gianlucarenzi/A1200KB/PlatePCB/amiga-keyboard-a500-a1200-bigass.png

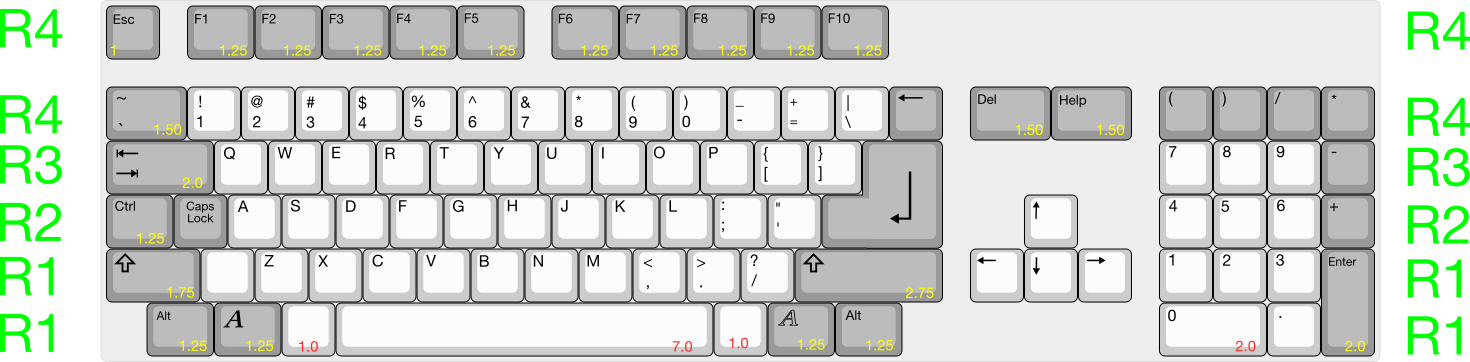
PlatePCB/amiga-keyboard-a500-a1200-bigass.png
