gianlucarenzi/A1200KB/3Dfiles/A1200.net case/rev3/Right base support.stl

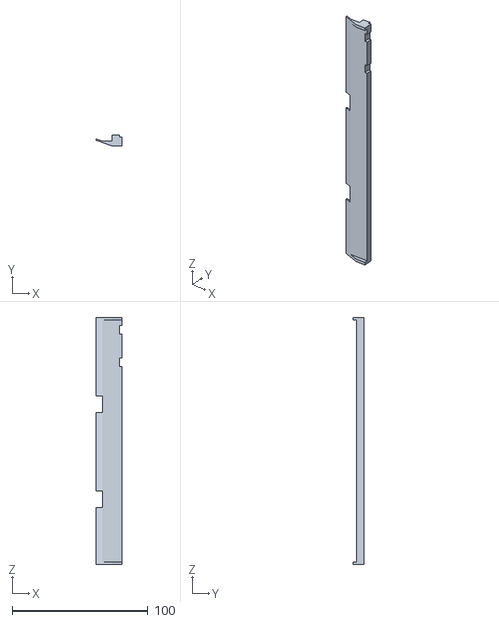
[picture p18: CAD file, 2023-02-19, an earlier design]
3Dfiles/A1200.net case/rev3/Right base support.stl
19.2 x 8.05 x 182.0
