gianlucarenzi/A1200KB/3Dfiles/A1200.net case/rev3/Brace insulator and spacer.stl

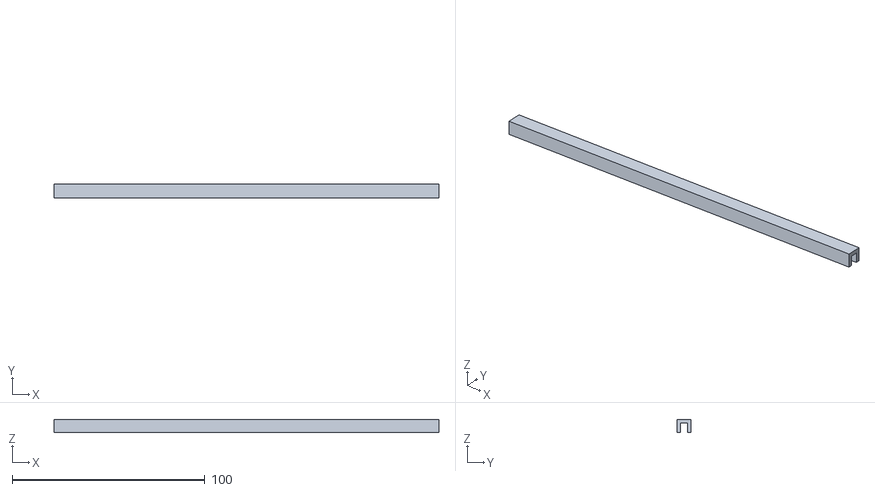
[picture p19: CAD file, 2023-02-19, an earlier design]
3Dfiles/A1200.net case/rev3/Brace insulator and spacer.stl
200.0 x 7.50 x 7.00
