gianlucarenzi/A1200KB/amiga_usb_mx/Core/Inc/host_driver.h

/*
Copyright 2011 Jun Wako <wakojun@gmail.com>

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
You should have received a copy of the GNU General Public License
along with this program.  If not, see <http://www.gnu.org/licenses/>.
*/

#ifndef HOST_DRIVER_H
#define HOST_DRIVER_H

#include <stdint.h>
#include "report.h"


typedef struct {
    uint8_t (*keyboard_leds)(void);
    void (*send_keyboard)(report_keyboard_t *);
    void (*send_mouse)(report_mouse_t *);
    void (*send_system)(uint16_t);
    void (*send_consumer)(uint16_t);
} host_driver_t;

#endif
