gianlucarenzi/A1200KB/amiga_usb_mx/Core/Src/action.c

/*
Copyright 2012,2013,2020 Jun Wako <wakojun@gmail.com>

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
You should have received a copy of the GNU General Public License
along with this program.  If not, see <http://www.gnu.org/licenses/>.
*/
#include "host.h"
#include "keycode.h"
#include "keyboard.h"
#include "mousekey.h"
#include "command.h"
#include "led.h"
#include "backlight.h"
#include "action_layer.h"
#include "action_tapping.h"
#include "action_macro.h"
#include "action_util.h"
#include "action.h"
#include "hook.h"
#include "wait.h"
#include "bootloader.h"

#ifdef DEBUG_ACTION
#include "debug.h"
#else
#include "nodebug.h"
#endif

static int debuglevel = DBG_INFO;

void action_exec(keyevent_t event)
{
    if (!IS_NOEVENT(event)) {
        dprint("EVENT: "); debug_event(event); dprintln();
        DBG_N("\r\n---- action_exec: start -----\r\n");
        DBG_N("EVENT: "); debug_event(event); dprintln();
        /*
         * This seems to be a BUG:
         * https://github.com/tmk/tmk_keyboard/blob/6271878a021fcf578b71e2b7e97cd43786efa7dd/tmk_core/common/action.c#L45
         */
        //hook_matrix_change(event);
    }

    keyrecord_t record = { .event = event };

#ifndef NO_ACTION_TAPPING
    action_tapping_process(record);
#else
    process_action(&record);
    if (!IS_NOEVENT(record.event)) {
        dprint("processed: "); debug_record(record); dprintln();
    }
#endif
}

void process_action(keyrecord_t *record)
{
	DBG_N("Called with %p\r\n", record);
    if (hook_process_action(record)) return;

    keyevent_t event = record->event;
#ifndef NO_ACTION_TAPPING
    uint8_t tap_count = record->tap.count;
#endif

    if (IS_NOEVENT(event)) {
    	DBG_N("No EVENT\r\n");
    	return;
    }

    action_t action = layer_switch_get_action(event);
    dprint("ACTION: "); debug_action(action);
#ifndef NO_ACTION_LAYER
    dprint(" layer_state: "); layer_debug();
    dprint(" default_layer_state: "); default_layer_debug();
#endif
    dprintln();

    DBG_N("SWITCH ACTION.KIND.ID %d\r\n", action.kind.id);
    switch (action.kind.id) {
        /* Key and Mods */
        case ACT_LMODS:
        case ACT_RMODS:
            {
                uint8_t mods = (action.kind.id == ACT_LMODS) ?  action.key.mods :
                                                                action.key.mods<<4;
                DBG_N("ACT_RMODS/ACT_RMODS: mods %d\r\n", mods);
                if (event.pressed) {
                    if (mods) {
                        add_weak_mods(mods);
                        send_keyboard_report();
                    }
                    register_code(action.key.code);
                } else {
                    unregister_code(action.key.code);
                    if (mods) {
                        del_weak_mods(mods);
                        send_keyboard_report();
                    }
                }
            }
            break;
#ifndef NO_ACTION_TAPPING
        case ACT_LMODS_TAP:
        case ACT_RMODS_TAP:
            {
                uint8_t mods = (action.kind.id == ACT_LMODS_TAP) ?  action.key.mods :
                                                                    action.key.mods<<4;
                switch (action.key.code) {
    #ifndef NO_ACTION_ONESHOT
                    case MODS_ONESHOT:
                        // Oneshot modifier
                        if (event.pressed) {
                            if (tap_count == 0) {
                                register_mods(mods);
                            }
                            else if (tap_count == 1) {
                                dprint("MODS_TAP: Oneshot: start\n");
                                set_oneshot_mods(mods);
                            }
                            else {
                                register_mods(mods);
                            }
                        } else {
                            if (tap_count == 0) {
                                clear_oneshot_mods();
                                unregister_mods(mods);
                            }
                            else if (tap_count == 1) {
                                // Retain Oneshot mods
                            }
                            else {
                                clear_oneshot_mods();
                                unregister_mods(mods);
                            }
                        }
                        break;
    #endif
                    case MODS_TAP_TOGGLE:
                        if (event.pressed) {
                            if (tap_count <= TAPPING_TOGGLE) {
                                if (mods & get_mods()) {
                                    dprint("MODS_TAP_TOGGLE: toggle mods off\n");
                                    unregister_mods(mods);
                                } else {
                                    dprint("MODS_TAP_TOGGLE: toggle mods on\n");
                                    register_mods(mods);
                                }
                            }
                        } else {
                            if (tap_count < TAPPING_TOGGLE) {
                                dprint("MODS_TAP_TOGGLE: release : unregister_mods\n");
                                unregister_mods(mods);
                            }
                        }
                        break;
                    default:
                        if (event.pressed) {
                            if (tap_count > 0) {
                                if (record->tap.interrupted) {
                                    dprint("MODS_TAP: Tap: Cancel: add_mods\n");
                                    // ad hoc: set 0 to cancel tap
                                    record->tap.count = 0;
                                    register_mods(mods);
                                } else {
                                    dprint("MODS_TAP: Tap: register_code\n");
                                    register_code(action.key.code);

                                    // Delay for MacOS #659
                                    if (action.key.code == KC_CAPSLOCK ||
                                            action.key.code == KC_NUMLOCK ||
                                            action.key.code == KC_SCROLLLOCK) {
                                        wait_ms(100);
                                    }
                                }
                            } else {
                                dprint("MODS_TAP: No tap: add_mods\n");
                                register_mods(mods);
                            }
                        } else {
                            if (tap_count > 0) {
                                dprint("MODS_TAP: Tap: unregister_code\n");
                                unregister_code(action.key.code);
                            } else {
                                dprint("MODS_TAP: No tap: add_mods\n");
                                unregister_mods(mods);
                            }
                        }
                        break;
                }
            }
            break;
#endif
#ifdef EXTRAKEY_ENABLE
        /* other HID usage */
        case ACT_USAGE:
            switch (action.usage.page) {
                case PAGE_SYSTEM:
                    if (event.pressed) {
                        host_system_send(action.usage.code);
                    } else {
                        host_system_send(0);
                    }
                    break;
                case PAGE_CONSUMER:
                    if (event.pressed) {
                        host_consumer_send(action.usage.code);
                    } else {
                        host_consumer_send(0);
                    }
                    break;
            }
            break;
#endif
#ifdef MOUSEKEY_ENABLE
        /* Mouse key */
        case ACT_MOUSEKEY:
            if (event.pressed) {
                mousekey_on(action.key.code);
                mousekey_send();
            } else {
                mousekey_off(action.key.code);
                mousekey_send();
            }
            break;
#endif
#ifndef NO_ACTION_LAYER
        case ACT_LAYER:
            if (action.layer_bitop.on == 0) {
                /* Default Layer Bitwise Operation */
                if (!event.pressed) {
                    uint8_t shift = action.layer_bitop.part*4;
                    uint32_t bits = ((uint32_t)action.layer_bitop.bits)<<shift;
                    uint32_t mask = (action.layer_bitop.xbit) ? ~(((uint32_t)0xf)<<shift) : 0;
                    switch (action.layer_bitop.op) {
                        case OP_BIT_AND: default_layer_and(bits | mask); break;
                        case OP_BIT_OR:  default_layer_or(bits | mask);  break;
                        case OP_BIT_XOR: default_layer_xor(bits | mask); break;
                        case OP_BIT_SET: default_layer_and(mask); default_layer_or(bits); break;
                    }
                }
            } else {
                /* Layer Bitwise Operation */
                if (event.pressed ? (action.layer_bitop.on & ON_PRESS) :
                                    (action.layer_bitop.on & ON_RELEASE)) {
                    uint8_t shift = action.layer_bitop.part*4;
                    uint32_t bits = ((uint32_t)action.layer_bitop.bits)<<shift;
                    uint32_t mask = (action.layer_bitop.xbit) ? ~(((uint32_t)0xf)<<shift) : 0;
                    switch (action.layer_bitop.op) {
                        case OP_BIT_AND: layer_and(bits | mask); break;
                        case OP_BIT_OR:  layer_or(bits | mask);  break;
                        case OP_BIT_XOR: layer_xor(bits | mask); break;
                        case OP_BIT_SET: layer_and(mask); layer_or(bits); break;
                    }
                }
            }
            break;
    #ifndef NO_ACTION_TAPPING
        case ACT_LAYER_TAP:
        case ACT_LAYER_TAP_EXT:
            switch (action.layer_tap.code) {
                case 0xc0 ... 0xdf:
                    /* layer On/Off with modifiers */
                    if (event.pressed) {
                        layer_on(action.layer_tap.val);
                        register_mods((action.layer_tap.code & 0x10) ?
                                (action.layer_tap.code & 0x0f) << 4 :
                                (action.layer_tap.code & 0x0f));
                    } else {
                        layer_off(action.layer_tap.val);
                        unregister_mods((action.layer_tap.code & 0x10) ?
                                (action.layer_tap.code & 0x0f) << 4 :
                                (action.layer_tap.code & 0x0f));
                    }
                    break;
                case OP_TAP_TOGGLE:
                    /* tap toggle */
                    if (event.pressed) {
                        if (tap_count < TAPPING_TOGGLE) {
                            layer_invert(action.layer_tap.val);
                        }
                    } else {
                        if (tap_count <= TAPPING_TOGGLE) {
                            layer_invert(action.layer_tap.val);
                        }
                    }
                    break;
                case OP_ON_OFF:
                    event.pressed ? layer_on(action.layer_tap.val) :
                                    layer_off(action.layer_tap.val);
                    break;
                case OP_OFF_ON:
                    event.pressed ? layer_off(action.layer_tap.val) :
                                    layer_on(action.layer_tap.val);
                    break;
                case OP_SET_CLEAR:
                    event.pressed ? layer_move(action.layer_tap.val) :
                                    layer_clear();
                    break;
                default:
                    /* tap key */
                    if (event.pressed) {
                        if (tap_count > 0) {
                            dprint("KEYMAP_TAP_KEY: Tap: register_code\n");
                            register_code(action.layer_tap.code);

                            // Delay for MacOS #659
                            if (action.layer_tap.code == KC_CAPSLOCK ||
                                    action.layer_tap.code == KC_NUMLOCK ||
                                    action.layer_tap.code == KC_SCROLLLOCK) {
                                wait_ms(100);
                            }
                        } else {
                            dprint("KEYMAP_TAP_KEY: No tap: On on press\n");
                            layer_on(action.layer_tap.val);
                        }
                    } else {
                        if (tap_count > 0) {
                            dprint("KEYMAP_TAP_KEY: Tap: unregister_code\n");
                            unregister_code(action.layer_tap.code);
                        } else {
                            dprint("KEYMAP_TAP_KEY: No tap: Off on release\n");
                            layer_off(action.layer_tap.val);
                        }
                    }
                    break;
            }
            break;
    #endif
#endif
        /* Extentions */
#ifndef NO_ACTION_MACRO
        case ACT_MACRO:
            action_macro_play(action_get_macro(record, action.func.id, action.func.opt));
            break;
#endif
#ifdef BACKLIGHT_ENABLE
        case ACT_BACKLIGHT:
            if (!event.pressed) {
                switch (action.backlight.opt) {
                    case BACKLIGHT_INCREASE:
                        backlight_increase();
                        break;
                    case BACKLIGHT_DECREASE:
                        backlight_decrease();
                        break;
                    case BACKLIGHT_TOGGLE:
                        backlight_toggle();
                        break;
                    case BACKLIGHT_STEP:
                        backlight_step();
                        break;
                    case BACKLIGHT_LEVEL:
                        backlight_level(action.backlight.level);
                        break;
                }
            }
            break;
#endif
        case ACT_COMMAND:
            switch (action.command.id) {
                case COMMAND_BOOTLOADER:
                    if (event.pressed) {
                        clear_keyboard();
                        wait_ms(50);
                        bootloader_jump();
                    }
                    break;
            }
            break;
#ifndef NO_ACTION_FUNCTION
        case ACT_FUNCTION:
            action_function(record, action.func.id, action.func.opt);
            break;
#endif
        default:
            break;
    }
}




/*
 * Utilities for actions.
 */
void register_code(uint8_t code)
{
	DBG_N("Called with: %d\r\n", code);
    if (code == KC_NO) {
        return;
    }

#ifdef LOCKING_SUPPORT_ENABLE
    else if (code == KC_LOCKING_CAPS ||
                code == KC_LOCKING_NUM ||
                code == KC_LOCKING_SCROLL) {
        uint8_t c, l;
        if (code == KC_LOCKING_CAPS) {
            c = KC_CAPSLOCK;
            l = 1<<USB_LED_CAPS_LOCK;
        } else if (code == KC_LOCKING_NUM) {
            c = KC_NUMLOCK;
            l = 1<<USB_LED_NUM_LOCK;
        } else if (code == KC_LOCKING_SCROLL) {
            c = KC_SCROLLLOCK;
            l = 1<<USB_LED_SCROLL_LOCK;
        }
#ifdef LOCKING_RESYNC_ENABLE
        // Resync: ignore if lock indicator is already on
        if (host_keyboard_leds() & l) return;
#endif
        add_key(c);
        send_keyboard_report();
        wait_ms(100); // Delay for MacOS #390
        del_key(c);
        send_keyboard_report();
    }
#endif

    else if IS_KEY(code) {
        // TODO: should push command_proc out of this block?
        if (command_proc(code)) return;

#ifndef NO_ACTION_ONESHOT
/* TODO: remove
        if (oneshot_state.mods && !oneshot_state.disabled) {
            uint8_t tmp_mods = get_mods();
            add_mods(oneshot_state.mods);

            add_key(code);
            send_keyboard_report();

            set_mods(tmp_mods);
            send_keyboard_report();
            oneshot_cancel();
        } else
*/
#endif
        {
            add_key(code);
            send_keyboard_report();
        }
    }
    else if IS_MOD(code) {
        add_mods(MOD_BIT(code));
        send_keyboard_report();
    }
    else if IS_SYSTEM(code) {
        host_system_send(KEYCODE2SYSTEM(code));
    }
    else if IS_CONSUMER(code) {
        host_consumer_send(KEYCODE2CONSUMER(code));
    }
}

void unregister_code(uint8_t code)
{
	DBG_N("Called with: %d\r\n", code);
    if (code == KC_NO) {
        return;
    }

#ifdef LOCKING_SUPPORT_ENABLE
    else if (code == KC_LOCKING_CAPS ||
                code == KC_LOCKING_NUM ||
                code == KC_LOCKING_SCROLL) {
        uint8_t c, l;
        if (code == KC_LOCKING_CAPS) {
            c = KC_CAPSLOCK;
            l = 1<<USB_LED_CAPS_LOCK;
        } else if (code == KC_LOCKING_NUM) {
            c = KC_NUMLOCK;
            l = 1<<USB_LED_NUM_LOCK;
        } else if (code == KC_LOCKING_SCROLL) {
            c = KC_SCROLLLOCK;
            l = 1<<USB_LED_SCROLL_LOCK;
        }
#ifdef LOCKING_RESYNC_ENABLE
        // Resync: ignore if lock indicator is already off
        if (!(host_keyboard_leds() & l)) return;
#endif
        add_key(c);
        send_keyboard_report();
        wait_ms(100); // Delay for MacOS #390
        del_key(c);
        send_keyboard_report();
    }
#endif

    else if IS_KEY(code) {
        del_key(code);
        send_keyboard_report();
    }
    else if IS_MOD(code) {
        del_mods(MOD_BIT(code));
        send_keyboard_report();
    }
    else if IS_SYSTEM(code) {
        host_system_send(0);
    }
    else if IS_CONSUMER(code) {
        host_consumer_send(0);
    }
}

void type_code(uint8_t code)
{
    register_code(code);
    unregister_code(code);
}

void register_mods(uint8_t mods)
{
	DBG_N("Called with: %d\r\n", mods);
    if (mods) {
        add_mods(mods);
        send_keyboard_report();
    }
}

void unregister_mods(uint8_t mods)
{
	DBG_N("Called with: %d\r\n", mods);
    if (mods) {
        del_mods(mods);
        send_keyboard_report();
    }
}

void clear_keyboard(void)
{
    clear_mods();
    clear_keyboard_but_mods();
}

void clear_keyboard_but_mods(void)
{
	DBG_N("Called\r\n");
    clear_weak_mods();
    clear_keys();
    send_keyboard_report();
#ifdef MOUSEKEY_ENABLE
    mousekey_clear();
    mousekey_send();
#endif
#ifdef EXTRAKEY_ENABLE
    host_system_send(0);
    host_consumer_send(0);
#endif
}

bool is_tap_key(keyevent_t event)
{
    if (IS_NOEVENT(event)) { return false; }

    action_t action = layer_switch_get_action(event);

    switch (action.kind.id) {
        case ACT_LMODS_TAP:
        case ACT_RMODS_TAP:
            switch (action.key.code) {
                case MODS_ONESHOT:
                case MODS_TAP_TOGGLE:
                case KC_A ... KC_EXSEL:                 // tap key
                case KC_LCTRL ... KC_RGUI:              // tap key
                    return true;
            }
        case ACT_LAYER_TAP:
        case ACT_LAYER_TAP_EXT:
            switch (action.layer_tap.code) {
                case 0xc0 ... 0xdf:         // with modifiers
                    return false;
                case KC_A ... KC_EXSEL:     // tap key
                case KC_LCTRL ... KC_RGUI:  // tap key
                case OP_TAP_TOGGLE:
                    return true;
            }
            return false;
        case ACT_MACRO:
        case ACT_FUNCTION:
            if (action.func.opt & FUNC_TAP) { return true; }
            return false;
    }
    return false;
}


/*
 * debug print
 */
void debug_event(keyevent_t event)
{
    dprintf("%04X%c(%u)", (event.key.row<<8 | event.key.col), (event.pressed ? 'd' : 'u'), event.time);
    DBG_N("%04X%c(%u)\r\n", (event.key.row<<8 | event.key.col), (event.pressed ? 'd' : 'u'), event.time);
}

void debug_record(keyrecord_t record)
{
    debug_event(record.event);
#ifndef NO_ACTION_TAPPING
    dprintf(":%u%c", record.tap.count, (record.tap.interrupted ? '-' : ' '));
#endif
}

void debug_action(action_t action)
{
    switch (action.kind.id) {
        case ACT_LMODS:             dprint("ACT_LMODS");             break;
        case ACT_RMODS:             dprint("ACT_RMODS");             break;
        case ACT_LMODS_TAP:         dprint("ACT_LMODS_TAP");         break;
        case ACT_RMODS_TAP:         dprint("ACT_RMODS_TAP");         break;
        case ACT_USAGE:             dprint("ACT_USAGE");             break;
        case ACT_MOUSEKEY:          dprint("ACT_MOUSEKEY");          break;
        case ACT_LAYER:             dprint("ACT_LAYER");             break;
        case ACT_LAYER_TAP:         dprint("ACT_LAYER_TAP");         break;
        case ACT_LAYER_TAP_EXT:     dprint("ACT_LAYER_TAP_EXT");     break;
        case ACT_MACRO:             dprint("ACT_MACRO");             break;
        case ACT_COMMAND:           dprint("ACT_COMMAND");           break;
        case ACT_FUNCTION:          dprint("ACT_FUNCTION");          break;
        default:                    dprint("UNKNOWN");               break;
    }
    dprintf("[%X:%02X]", action.kind.param>>8, action.kind.param&0xff);
}
