gianlucarenzi/A1200KB/amiga_usb_mx/Core/Inc/print.h

/* Copyright 2012 Jun Wako <wakojun@gmail.com> */
/* Very basic print functions, intended to be used with usb_debug_only.c
 * http://www.pjrc.com/teensy/
 * Copyright (c) 2008 PJRC.COM, LLC
 *
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
 * THE SOFTWARE IS PROVIDED "AS IS", WITHOUT WARRANTY OF ANY KIND, EXPRESS OR
 * IMPLIED, INCLUDING BUT NOT LIMITED TO THE WARRANTIES OF MERCHANTABILITY,
 * FITNESS FOR A PARTICULAR PURPOSE AND NONINFRINGEMENT. IN NO EVENT SHALL THE
 * AUTHORS OR COPYRIGHT HOLDERS BE LIABLE FOR ANY CLAIM, DAMAGES OR OTHER
 * LIABILITY, WHETHER IN AN ACTION OF CONTRACT, TORT OR OTHERWISE, ARISING FROM,
 * OUT OF OR IN CONNECTION WITH THE SOFTWARE OR THE USE OR OTHER DEALINGS IN
 * THE SOFTWARE.
 */

#ifndef PRINT_H__
#define PRINT_H__ 1

#include <stdint.h>
#include <stdbool.h>
#include "util.h"




#ifndef NO_PRINT


#if defined(__AVR__)

	#include "avr/xprintf.h"
	#define print(s)    xputs(PSTR(s))
	#define println(s)  xputs(PSTR(s "\r\n"))

	#ifdef __cplusplus
	extern "C"
	#endif
	/* function pointer of sendchar to be used by print utility */
	void print_set_sendchar(int8_t (*print_sendchar_func)(uint8_t));

#elif defined(PROTOCOL_CHIBIOS) /* __AVR__ */

	#include "chibios/printf.h"

	#define print(s)    printf(s)
	#define println(s)  printf(s "\r\n")
	#define xprintf  printf

#elif defined(__arm__) /* __AVR__ */

	#define xprintf(fmt, args...) printf(fmt, ## args)
	#define print(s)    xprintf(s)
	#define println(s)  xprintf(s "\r\n")

	/* TODO: to select output destinations: UART/USBSerial */
	#define print_set_sendchar(func)

#endif /* __AVR__ */


/* decimal */
#define print_dec(i)                xprintf("%u", i)
#define print_decs(i)               xprintf("%d", i)
/* hex */
#define print_hex4(i)               xprintf("%X", i)
#define print_hex8(i)               xprintf("%02X", i)
#define print_hex16(i)              xprintf("%04X", i)
#define print_hex32(i)              xprintf("%08lX", i)
/* binary */
#ifdef __AVR__
#define print_bin4(i)               xprintf("%04b", i)
#define print_bin8(i)               xprintf("%08b", i)
#define print_bin16(i)              xprintf("%016b", i)
#define print_bin32(i)              xprintf("%032lb", i)
#define print_bin_reverse8(i)       xprintf("%08b", bitrev(i))
#define print_bin_reverse16(i)      xprintf("%016b", bitrev(i))
#define print_bin_reverse32(i)      xprintf("%032lb", bitrev(i))
#define print_val_bin8(v)           xprintf(#v ": %08b\n", v)
#define print_val_bin16(v)          xprintf(#v ": %016b\n", v)
#define print_val_bin32(v)          xprintf(#v ": %032lb\n", v)
#define print_val_bin_reverse8(v)   xprintf(#v ": %08b\n", bitrev(v))
#define print_val_bin_reverse16(v)  xprintf(#v ": %016b\n", bitrev16(v))
#define print_val_bin_reverse32(v)  xprintf(#v ": %032lb\n", bitrev32(v))
#endif
#ifdef __arm__
extern void xprintfbin(uint32_t val, int n_bits);
extern void xprintfbin_rev(uint32_t val, int n_bits);
#define print_bin4(i)               xprintfbin(i, 4)
#define print_bin8(i)               xprintfbin(i, 8)
#define print_bin16(i)              xprintfbin(i, 16)
#define print_bin32(i)              xprintfbin(i, 32)
#define print_bin_reverse8(i)       xprintfbin_rev(i, 8)
#define print_bin_reverse16(i)      xprintfbin_rev(i, 16)
#define print_bin_reverse32(i)      xprintfbin_rev(i, 32)
#endif
/* print value utility */
#define print_val_dec(v)            xprintf(#v ": %u\n", v)
#define print_val_decs(v)           xprintf(#v ": %d\n", v)
#define print_val_hex8(v)           xprintf(#v ": %X\n", v)
#define print_val_hex16(v)          xprintf(#v ": %02X\n", v)
#define print_val_hex32(v)          xprintf(#v ": %04lX\n", v)

#else   /* NO_PRINT */

#define xprintf(s,...)              ((void)0)
#define print(s)                    ((void)0)
#define println(s)                  ((void)0)
#define print_set_sendchar(func)    ((void)0)
#define print_dec(data)             ((void)0)
#define print_decs(data)            ((void)0)
#define print_hex4(data)            ((void)0)
#define print_hex8(data)            ((void)0)
#define print_hex16(data)           ((void)0)
#define print_hex32(data)           ((void)0)
#define print_bin4(data)            ((void)0)
#define print_bin8(data)            ((void)0)
#define print_bin16(data)           ((void)0)
#define print_bin32(data)           ((void)0)
#define print_bin_reverse8(data)    ((void)0)
#define print_bin_reverse16(data)   ((void)0)
#define print_bin_reverse32(data)   ((void)0)
#define print_val_dec(v)            ((void)0)
#define print_val_decs(v)           ((void)0)
#define print_val_hex8(v)           ((void)0)
#define print_val_hex16(v)          ((void)0)
#define print_val_hex32(v)          ((void)0)
#define print_val_bin8(v)           ((void)0)
#define print_val_bin16(v)          ((void)0)
#define print_val_bin32(v)          ((void)0)
#define print_val_bin_reverse8(v)   ((void)0)
#define print_val_bin_reverse16(v)  ((void)0)
#define print_val_bin_reverse32(v)  ((void)0)
#define init_printf(s,ss)           ((void)0)

#endif  /* NO_PRINT */


/* Backward compatiblitly for old name */
#define pdec(data)              print_dec(data)
#define pdec16(data)            print_dec(data)
#define phex(data)              print_hex8(data)
#define phex16(data)            print_hex16(data)
#define pbin(data)              print_bin8(data)
#define pbin16(data)            print_bin16(data)
#define pbin_reverse(data)      print_bin_reverse8(data)
#define pbin_reverse16(data)    print_bin_reverse16(data)


#endif
