gianlucarenzi/A1200KB/amiga_usb_mx/Core/Inc/debug.h

/*
 * $Id: debug.h,v 1.1 2016/01/12 09:17:22 gianluca Exp $
 */
#ifndef __DEBUG_H__
#define __DEBUG_H__

#include <stdio.h>
#include <stdint.h>
#include <stdbool.h>
#include "print.h"

#ifdef __cplusplus
extern "C" {
#endif

/*
 * Debug output control
 */
typedef union {
	struct {
		bool enable:1;
		bool matrix:1;
		bool keyboard:1;
		bool mouse:1;
		uint8_t reserved:4;
	};
	uint8_t raw;
} debug_config_t;

extern debug_config_t debug_config;

#ifdef __cplusplus
}
#endif

/* for backward compatibility */
#define debug_enable    (debug_config.enable)
#define debug_matrix    (debug_config.matrix)
#define debug_keyboard  (debug_config.keyboard)
#define debug_mouse     (debug_config.mouse)


/*
 * Debug print utils
 */
#ifndef NO_DEBUG

#define dprint(s)                   do { if (debug_enable) print(s); } while (0)
#define dprintln(s)                 do { if (debug_enable) println(s); } while (0)
#define dprintf(fmt, ...)           do { if (debug_enable) xprintf(fmt, ##__VA_ARGS__); } while (0)
#define dmsg(s)                     dprintf("%s at %s: %S\n", __FILE__, __LINE__, PSTR(s))

/* Deprecated. DO NOT USE these anymore, use dprintf instead. */
#define debug(s)                    do { if (debug_enable) print(s); } while (0)
#define debugln(s)                  do { if (debug_enable) println(s); } while (0)
#define debug_msg(s)                do { \
    if (debug_enable) { \
        print(__FILE__); print(" at "); print_dec(__LINE__); print(" in "); print(": "); print(s); \
    } \
} while (0)
#define debug_dec(data)             do { if (debug_enable) print_dec(data); } while (0)
#define debug_decs(data)            do { if (debug_enable) print_decs(data); } while (0)
#define debug_hex4(data)            do { if (debug_enable) print_hex4(data); } while (0)
#define debug_hex8(data)            do { if (debug_enable) print_hex8(data); } while (0)
#define debug_hex16(data)           do { if (debug_enable) print_hex16(data); } while (0)
#define debug_hex32(data)           do { if (debug_enable) print_hex32(data); } while (0)
#define debug_bin8(data)            do { if (debug_enable) print_bin8(data); } while (0)
#define debug_bin16(data)           do { if (debug_enable) print_bin16(data); } while (0)
#define debug_bin32(data)           do { if (debug_enable) print_bin32(data); } while (0)
#define debug_bin_reverse8(data)    do { if (debug_enable) print_bin_reverse8(data); } while (0)
#define debug_bin_reverse16(data)   do { if (debug_enable) print_bin_reverse16(data); } while (0)
#define debug_bin_reverse32(data)   do { if (debug_enable) print_bin_reverse32(data); } while (0)
#define debug_hex(data)             debug_hex8(data)
#define debug_bin(data)             debug_bin8(data)
#define debug_bin_reverse(data)     debug_bin8(data)

#else /* NO_DEBUG */

#define dprint(s)                   ((void)0)
#define dprintln(s)                 ((void)0)
#define dprintf(fmt, ...)           ((void)0)
#define dmsg(s)                     ((void)0)
#define debug(s)                    ((void)0)
#define debugln(s)                  ((void)0)
#define debug_msg(s)                ((void)0)
#define debug_dec(data)             ((void)0)
#define debug_decs(data)            ((void)0)
#define debug_hex4(data)            ((void)0)
#define debug_hex8(data)            ((void)0)
#define debug_hex16(data)           ((void)0)
#define debug_hex32(data)           ((void)0)
#define debug_bin8(data)            ((void)0)
#define debug_bin16(data)           ((void)0)
#define debug_bin32(data)           ((void)0)
#define debug_bin_reverse8(data)    ((void)0)
#define debug_bin_reverse16(data)   ((void)0)
#define debug_bin_reverse32(data)   ((void)0)
#define debug_hex(data)             ((void)0)
#define debug_bin(data)             ((void)0)
#define debug_bin_reverse(data)     ((void)0)

#endif /* NO_DEBUG */

/* ANSI Eye-Candy ;-) */
#define ANSI_RED    "\x1b[31m"
#define ANSI_GREEN  "\x1b[32m"
#define ANSI_YELLOW "\x1b[1;33m"
#define ANSI_BLUE   "\x1b[1;34m"
#define ANSI_RESET  "\x1b[0m"

#define printR(fmt, args...) \
	{\
		printf(fmt, ## args); \
	}

#define printRaw(type, fmt, args...) \
	{\
		printf("%s " type " (%s): " fmt, __FILE__, __func__, ## args); \
	}

#define DBG_N(fmt, args...) \
  { if (debuglevel >= DBG_NOISY) {\
		printf(ANSI_YELLOW); \
		printRaw("NOISY", fmt,## args); \
		printf(ANSI_RESET); \
	} \
  }

#define DBG_V(fmt, args...) \
  { if (debuglevel >= DBG_VERBOSE) {\
		printf(ANSI_BLUE); \
		printRaw("VERBOSE", fmt,## args); \
		printf(ANSI_RESET); \
	} \
  }

#define DBG_I(fmt, args...) \
  { if (debuglevel >= DBG_INFO) {\
		printf(ANSI_GREEN); \
		printRaw("INFO", fmt,## args); \
		printf(ANSI_RESET); \
	} \
  }

#define DBG_E(fmt, args...) \
  { \
	printf(ANSI_RED); \
	printRaw("ERR", fmt, ## args); \
	printf(ANSI_RESET); \
  }

#define DBG_ERROR   0
#define DBG_INFO    1
#define DBG_VERBOSE 2
#define DBG_NOISY   3

#ifdef __cplusplus
}
#endif

#endif
