gianlucarenzi/A1200KB/amiga_usb_mx/Core/Src/syscall.c

#include <errno.h>
#include <sys/unistd.h> // STDOUT_FILENO, STDERR_FILENO
#include "syscall.h"
#include <stm32f4xx_hal.h> // per HAL_StatusTypeDef
#include "debug.h"

static t_syscall_status uart_initialize = SYSCALL_NOTREADY;
static UART_HandleTypeDef *uart = NULL;
static int debuglevel = DBG_ERROR;

void _write_ready(t_syscall_status rdy, UART_HandleTypeDef *ptr)
{
	if (ptr != NULL)
	{
		uart_initialize = rdy;
		uart = ptr;
	}
}

int _write(int file, char *data, int len)
{
	HAL_StatusTypeDef status = HAL_OK - 1;

	if ((file != STDOUT_FILENO) && (file != STDERR_FILENO))
	{
		errno = EBADF;
		return -1;
	}

	if (uart_initialize == SYSCALL_READY)
	{
		if (uart != NULL)
		{
			// arbitrary timeout 1000
			status = HAL_UART_Transmit(uart, (uint8_t*)data, len, 1000);
		}
	}

	// return # of bytes written - as best we can tell
	return (status == HAL_OK ? len : 0);
}

static uint32_t timertick_start_ms = 0;
void timer_start(void)
{
	// When timer starts get the realtime system tick
	timertick_start_ms = HAL_GetTick();
}

// I hate this delay because they are clockspeed dependent!!!
#define delayUS_ASM(us) do {\
	asm volatile (	"MOV R0,%[loops]\n\t"\
			"1: \n\t"\
			"SUB R0, #1\n\t"\
			"CMP R0, #0\n\t"\
			"BNE 1b \n\t" : : [loops] "r" (16*us) : "memory"\
		      );\
} while(0)

void udelay(uint32_t micros)
{
	DBG_N("Enter with: %lu\n", micros);
	if (micros > 0)
	{
		/* Go to number of cycles for system */
		DBG_N("MICROS: %lu\r\n", micros);
		delayUS_ASM(micros);
	}
	DBG_N("Exit\r\n");
}

void mdelay(uint32_t millis)
{
	HAL_Delay(millis);
}
