gianlucarenzi/A1200KB/amiga_usb_mx/Core/Inc/syscall.h

#ifndef __SYSCALL_INCLUDED__
#define __SYSCALL_INCLUDED__

#include <stdio.h>
#include <stm32f4xx_hal.h>
#include "stm32f4xx_it.h"

typedef enum {
	SYSCALL_NOTREADY,
	SYSCALL_READY,
} t_syscall_status;

extern void _write_ready(t_syscall_status rdy, UART_HandleTypeDef *ptr);
extern int _write(int file, char *data, int len);
/**
 * blocking functions!
 **/
extern void mdelay(uint32_t millis);
extern void udelay(uint32_t micros);

#endif
