gianlucarenzi/A1200KB/amiga_usb_mx/Core/Inc/atari_config.h

#ifndef __CONFIG_ATARI_INCLUDED__
#define __CONFIG_ATARI_INCLUDED__

#include "main.h"
#include "keyboard.h"
#include "keycode.h"
#include "action.h"

#define KEYBOARD_COLUMNS 13
#define KEYBOARD_ROWS    9

extern const uint8_t keymaps[][KEYBOARD_ROWS][KEYBOARD_COLUMNS];
extern gpioPort_t lut_row[ KEYBOARD_ROWS ];
extern gpioPort_t lut_col[ KEYBOARD_COLUMNS ];

static const action_t PROGMEM fn_actions[1] = {};

#endif
