gianlucarenzi/A1200KB/amiga_usb_mx/Core/Inc/matrix.h

/*
Based on original concept by:
Copyright 2011 Jun Wako <wakojun@gmail.com>

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
You should have received a copy of the GNU General Public License
along with this program.  If not, see <http://www.gnu.org/licenses/>.
*/

#ifndef MATRIX_H
#define MATRIX_H

#include <stdint.h>
#include <stdbool.h>
#include <config.h>

#if (MATRIX_COLS <= 8)
typedef  uint8_t    matrix_row_t;
#elif (MATRIX_COLS <= 16)
typedef  uint16_t   matrix_row_t;
#elif (MATRIX_COLS <= 32)
typedef  uint32_t   matrix_row_t;
#else
#error "MATRIX_COLS: invalid value"
#endif

#if (MATRIX_ROWS > 255)
#error "MATRIX_ROWS must not exceed 255"
#endif

#define MATRIX_IS_ON(row, col)  (matrix_get_row(row) && (1<<col))


#ifdef __cplusplus
extern "C" {
#endif

/* number of matrix rows */
uint8_t matrix_rows(void);
/* number of matrix columns */
uint8_t matrix_cols(void);
/* should be called at early stage of startup before matrix_init.(optional) */
void matrix_setup(void);
/* intialize matrix for scaning. */
void matrix_init(void);
/* scan all key states on matrix */
uint8_t matrix_scan(void);
/* whether modified from previous scan. used after matrix_scan. */
bool matrix_is_modified(void) __attribute__ ((deprecated));
/* whether a swtich is on */
bool matrix_is_on(uint8_t row, uint8_t col);
/* matrix state on row */
matrix_row_t matrix_get_row(uint8_t row);
/* print matrix for debug */
void matrix_print(void);
/* clear matrix */
void matrix_clear(void);
/* print a single matrix row */
void matrix_print_row(uint8_t row);


#ifdef MATRIX_HAS_GHOST
bool matrix_has_ghost_in_row(uint8_t row);
#endif

/* power control */
void matrix_power_up(void);
void matrix_power_down(void);

#ifdef __cplusplus
}
#endif

#endif
